modxmodfurnishings/modxmod-main/labs/experimental/F0617_TableInsert_StandBack.STEP

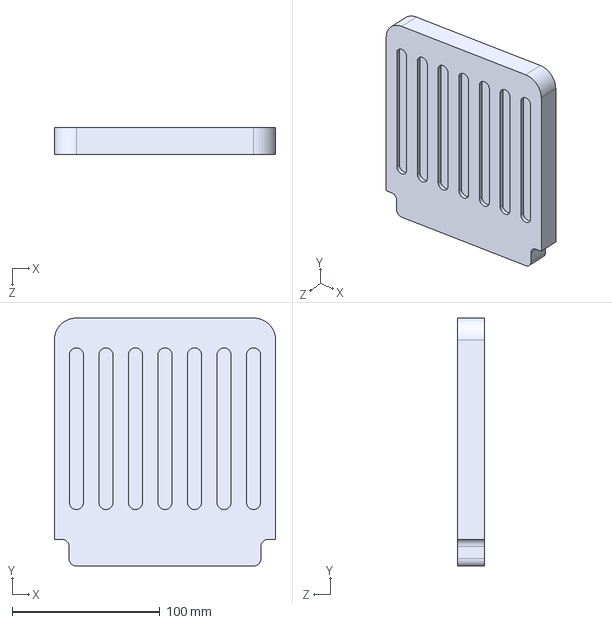
[picture p33: CAD file, 2024-06-18]
labs/experimental/F0617_TableInsert_StandBack.STEP
150.0 x 168.0 x 18.0 mm
