modxmodfurnishings/modxmod-main/labs/experimental/F0529_Span100_Wood_C2.STL

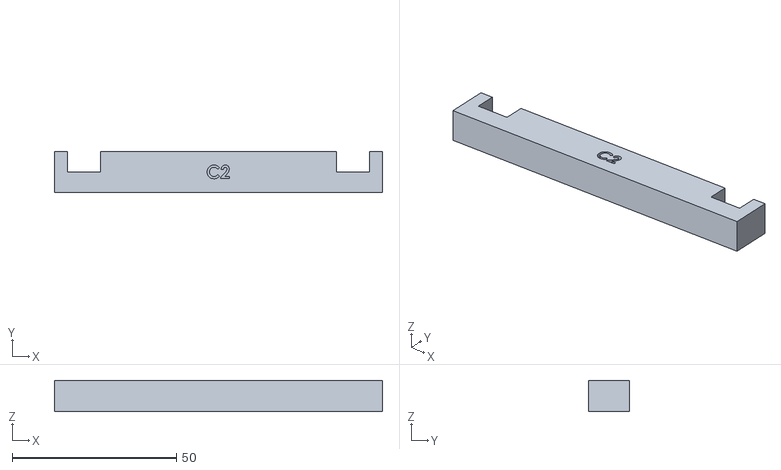
[picture p34: CAD file, 2024-05-30]
labs/experimental/F0529_Span100_Wood_C2.STL
100.0 x 12.6 x 9.50
