modxmodfurnishings/modxmod-main/labs/experimental/F0529_PostPlug_C.STL

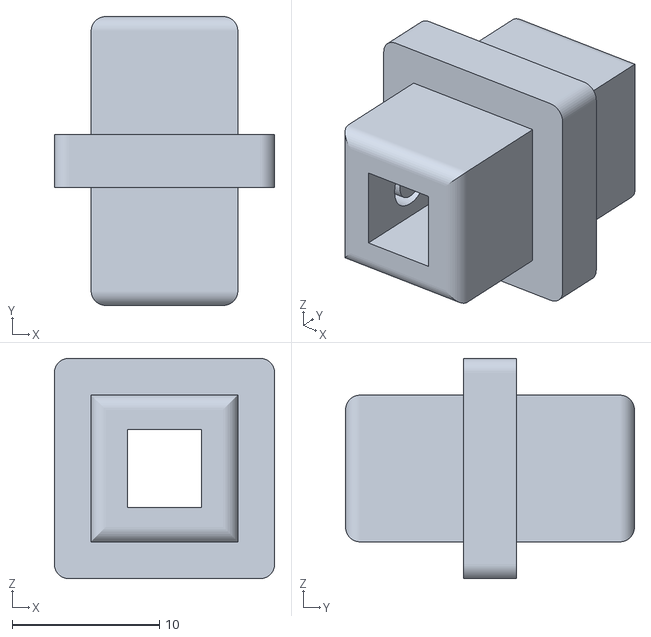
[picture p35: CAD file, 2024-05-30]
labs/experimental/F0529_PostPlug_C.STL
14.9 x 19.6 x 14.9
