modxmodfurnishings/modxmod-main/labs/experimental/F0529_Post80_Wood_C.STL

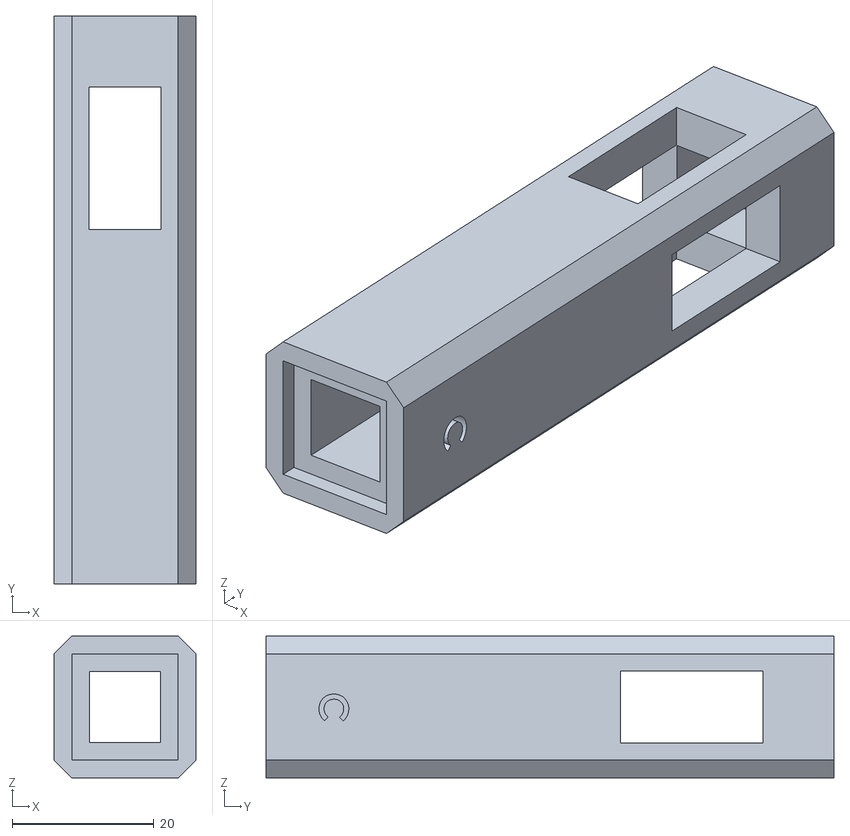
[picture p36: CAD file, 2024-05-30]
labs/experimental/F0529_Post80_Wood_C.STL
20.0 x 80.0 x 20.0
