modxmodfurnishings/modxmod-main/labs/experimental/Drawer Front XLatch Top (1).stl

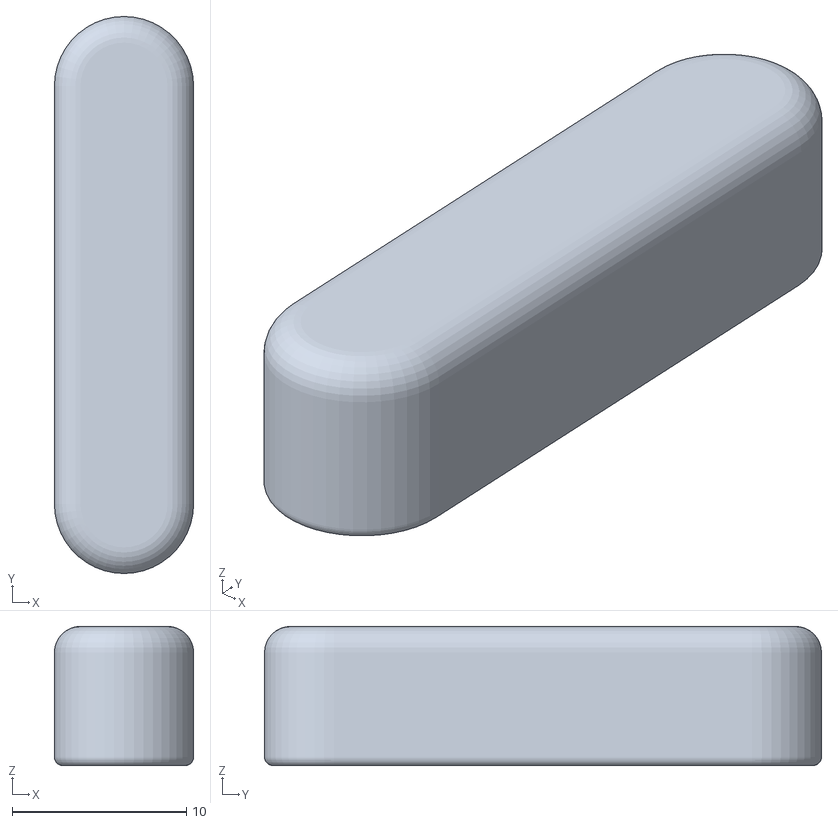
[picture p37: CAD file, 2024-04-15]
labs/experimental/Drawer Front XLatch Top (1).stl
8.00 x 32.0 x 8.00
