modxmodfurnishings/modxmod-main/labs/experimental/CabFrame Bar2.stl

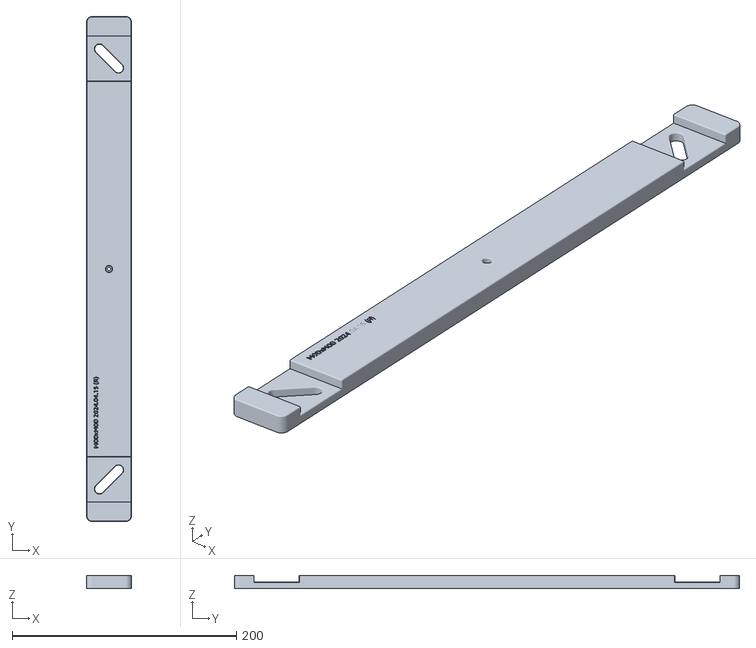
[picture p38: CAD file, 2024-04-15]
labs/experimental/CabFrame Bar2.stl
40.0 x 450.0 x 12.0
