modxmodfurnishings/modxmod-main/labs/experimental/CabFrame Corner2 (1).stl

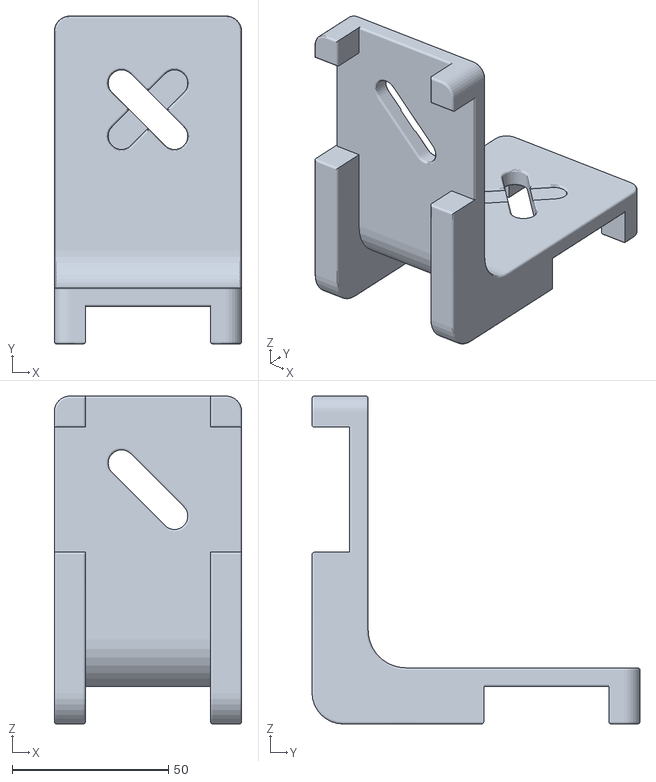
[picture p39: CAD file, 2024-04-15]
labs/experimental/CabFrame Corner2 (1).stl
60.0 x 105.0 x 105.0
