modxmodfurnishings/modxmod-main/labs/experimental/Drawer Front XLatch Test Wall 1 (1).stl

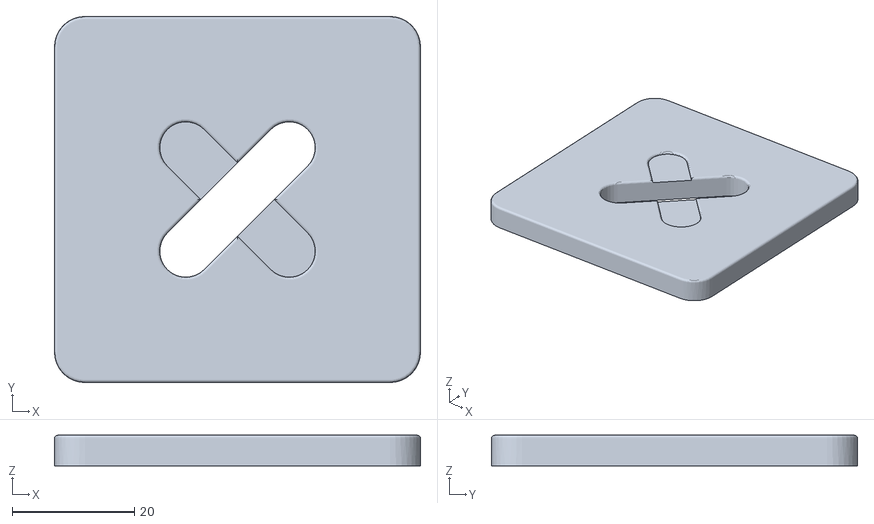
[picture p40: CAD file, 2024-04-15]
labs/experimental/Drawer Front XLatch Test Wall 1 (1).stl
60.0 x 60.0 x 5.00
