modxmodfurnishings/modxmod-main/labs/experimental/FurnNightst02a v5.stl

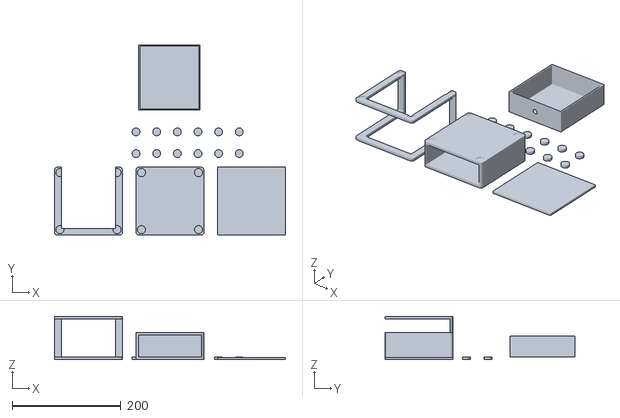
[picture p41: CAD file, 2024-03-26]
labs/experimental/FurnNightst02a v5.stl
425.0 x 350.0 x 80.0
