modxmodfurnishings/modxmod-main/labs/experimental/Pulls1 v8.stl

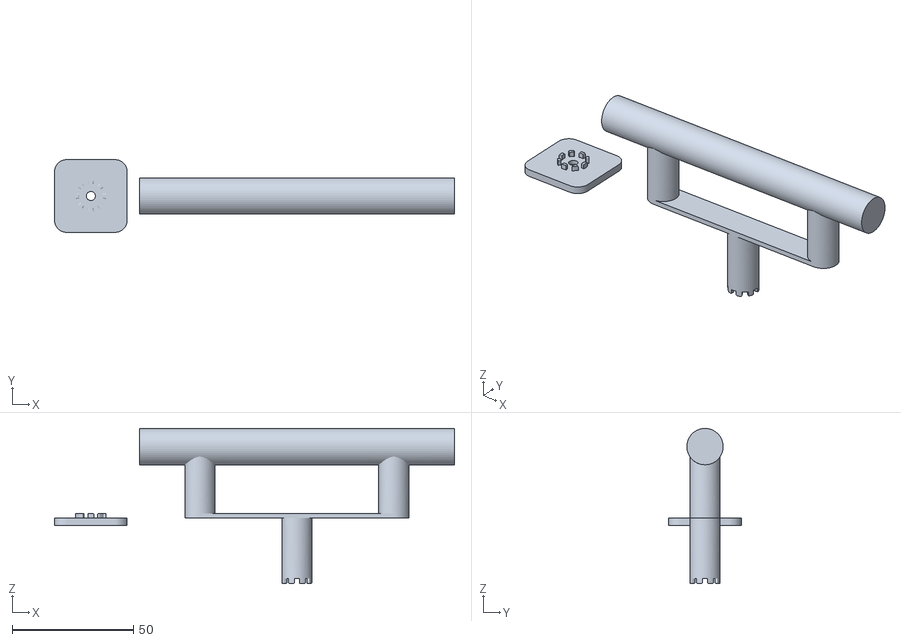
[picture p42: CAD file, 2024-03-26]
labs/experimental/Pulls1 v8.stl
165.0 x 30.0 x 64.0
