modxmodfurnishings/modxmod-main/labs/experimental/Pulls1 v6.3mf

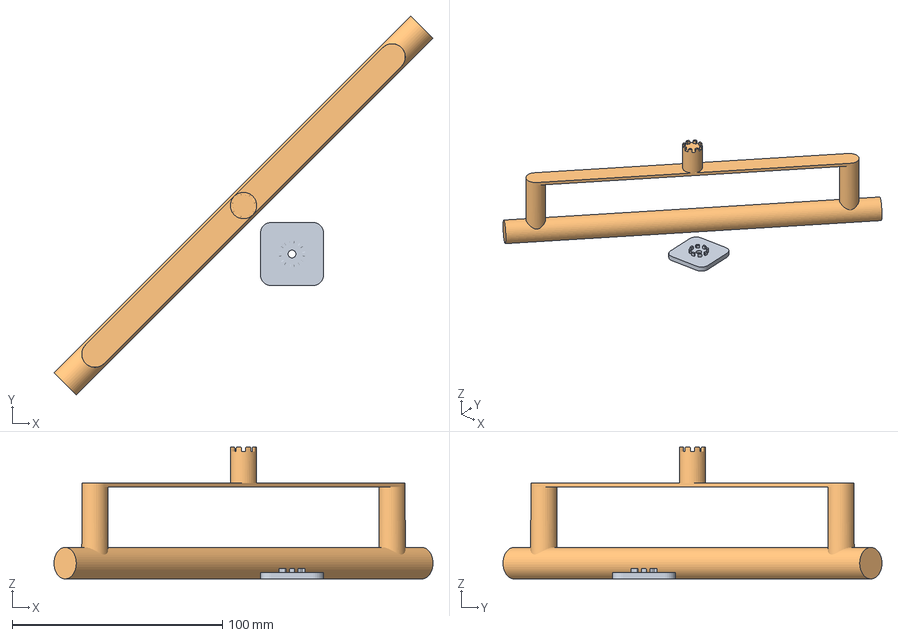
[picture p43: CAD file, 2024-03-26]
labs/experimental/Pulls1 v6.3mf
180.3 x 180.3 x 62.7 mm
Pulls1 v6.stl_1
Pulls1 v6.stl_2
