modxmodfurnishings/modxmod-main/labs/experimental/Furn1 v8.stl

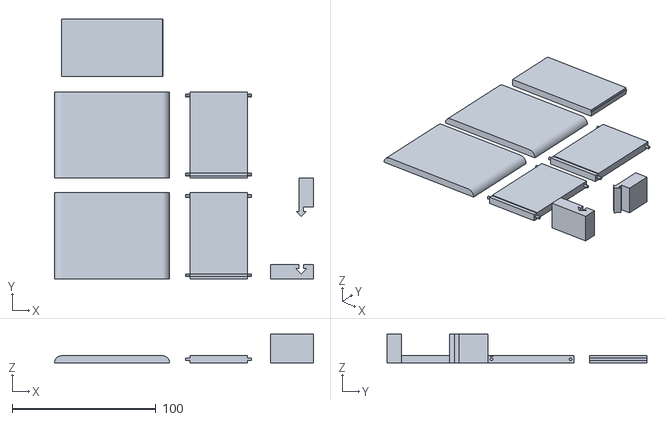
[picture p44: CAD file, 2024-03-24]
labs/experimental/Furn1 v8.stl
180.0 x 180.6 x 20.0
