modxmodfurnishings/modxmod-main/labs/experimental/Aligner v1.stl

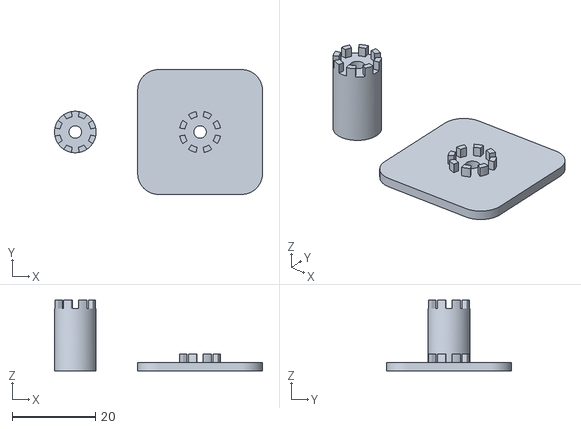
[picture p45: CAD file, 2024-03-24]
labs/experimental/Aligner v1.stl
50.0 x 30.0 x 17.0
