modxmodfurnishings/modxmod-main/labs/experimental/TeethKnobTri1.stl

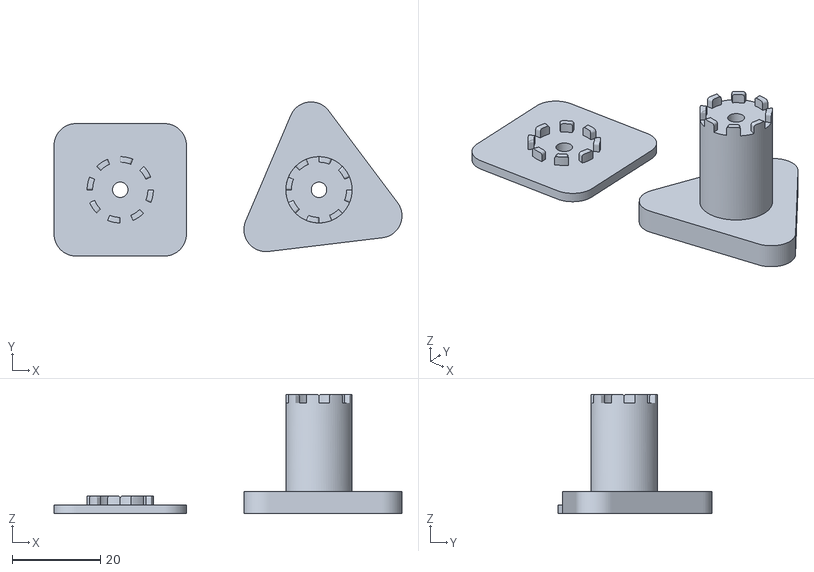
[picture p46: CAD file, 2024-03-24]
labs/experimental/TeethKnobTri1.stl
78.8 x 34.9 x 27.0
