modxmodfurnishings/modxmod-main/labs/experimental/Furn2 v6 bamboo front only.3mf

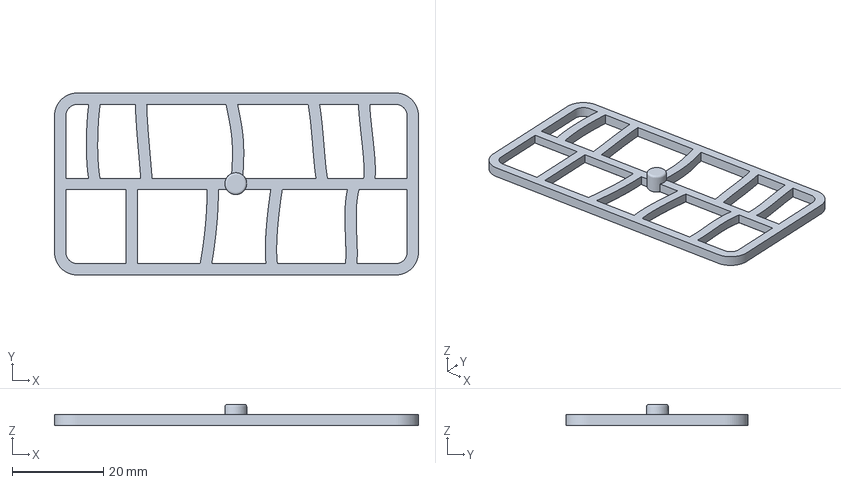
[picture p47: CAD file, 2024-03-24]
labs/experimental/Furn2 v6 bamboo front only.3mf
79.7 x 39.9 x 4.70 mm
