modxmodfurnishings/modxmod-main/labs/experimental/Furn3 v21.stl

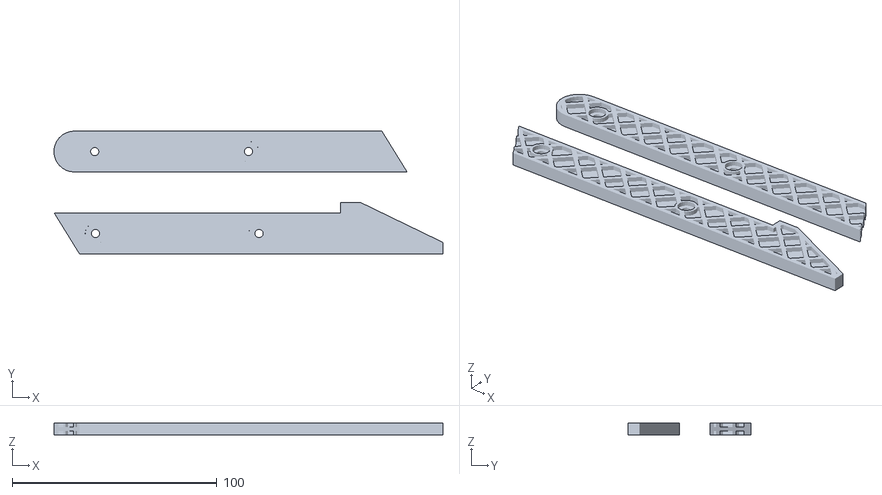
[picture p48: CAD file, 2024-03-24]
labs/experimental/Furn3 v21.stl
189.9 x 60.0 x 6.00
