modxmodfurnishings/modxmod-main/labs/experimental/Furn2 v6.stl

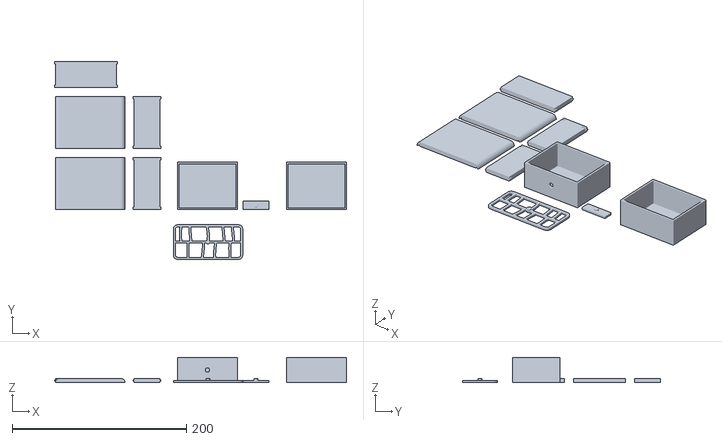
[picture p49: CAD file, 2024-03-24]
labs/experimental/Furn2 v6.stl
335.0 x 227.0 x 29.0
