modxmodfurnishings/modxmod-main/labs/experimental/Furn3 v3.step

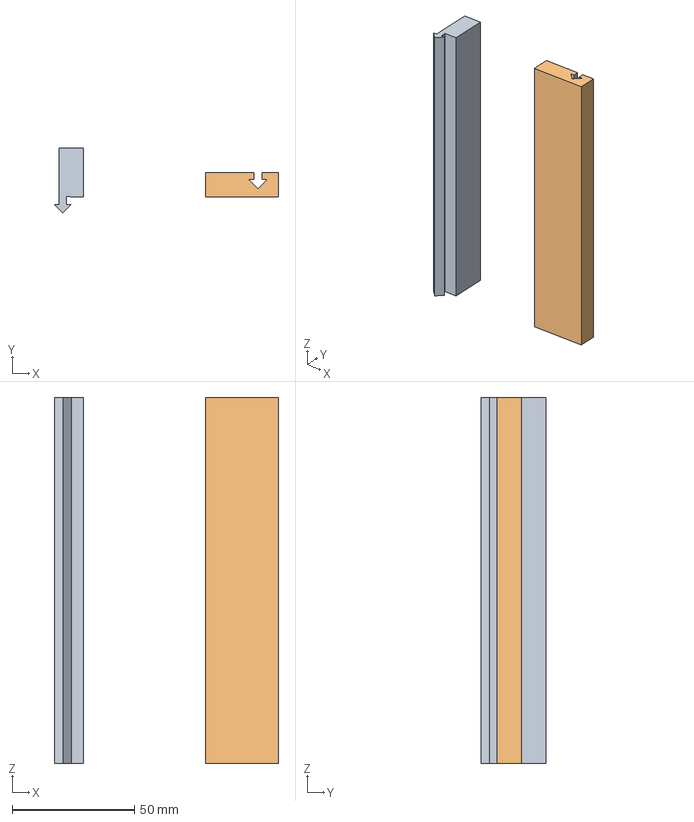
[picture p50: CAD file, 2024-03-24]
labs/experimental/Furn3 v3.step
92.0 x 26.5 x 150.0 mm
