modxmodfurnishings/modxmod-main/labs/experimental/F0605-full-assembly.png

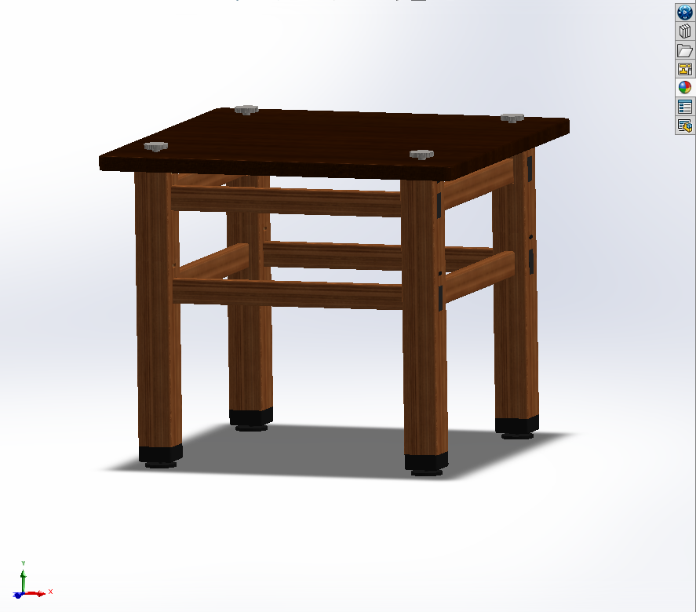
labs/experimental/F0605-full-assembly.png
