modxmodfurnishings/modxmod-main/labs/experimental/F0605-post-assembly.png

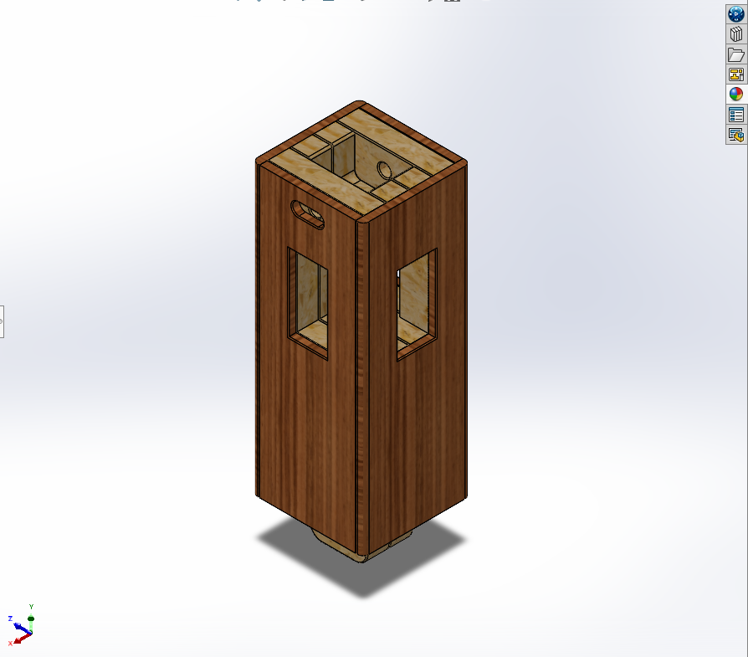
labs/experimental/F0605-post-assembly.png
