modxmodfurnishings/modxmod-main/labs/experimental/B384-exploded.jpg

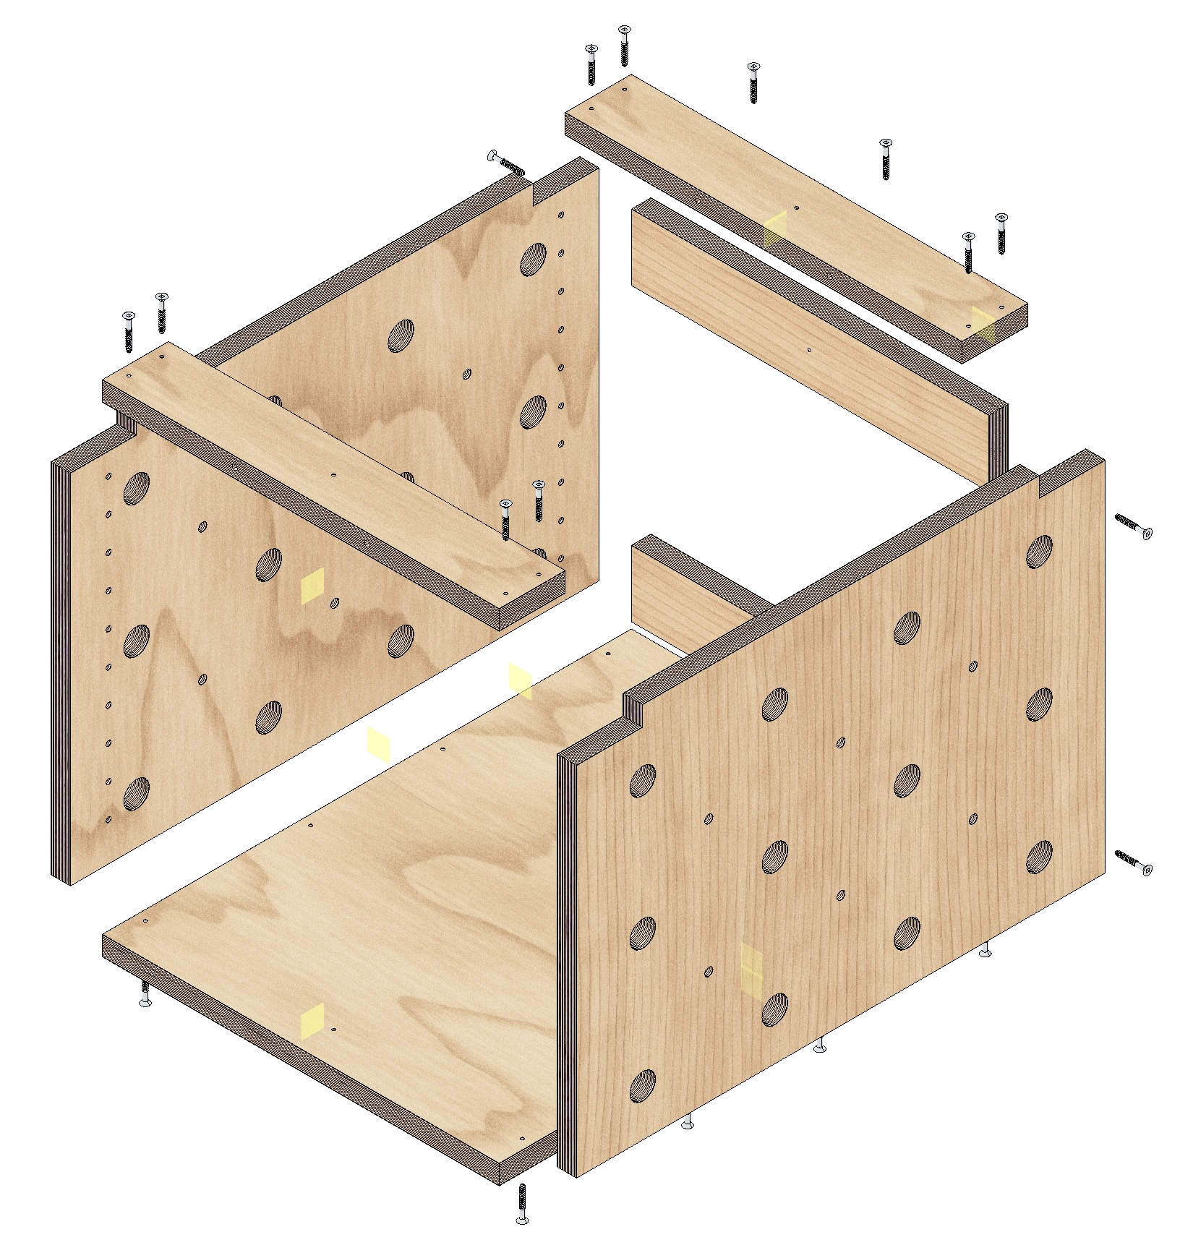
labs/experimental/B384-exploded.jpg
