modxmodfurnishings/modxmod-main/labs/experimental/B384-together.jpg

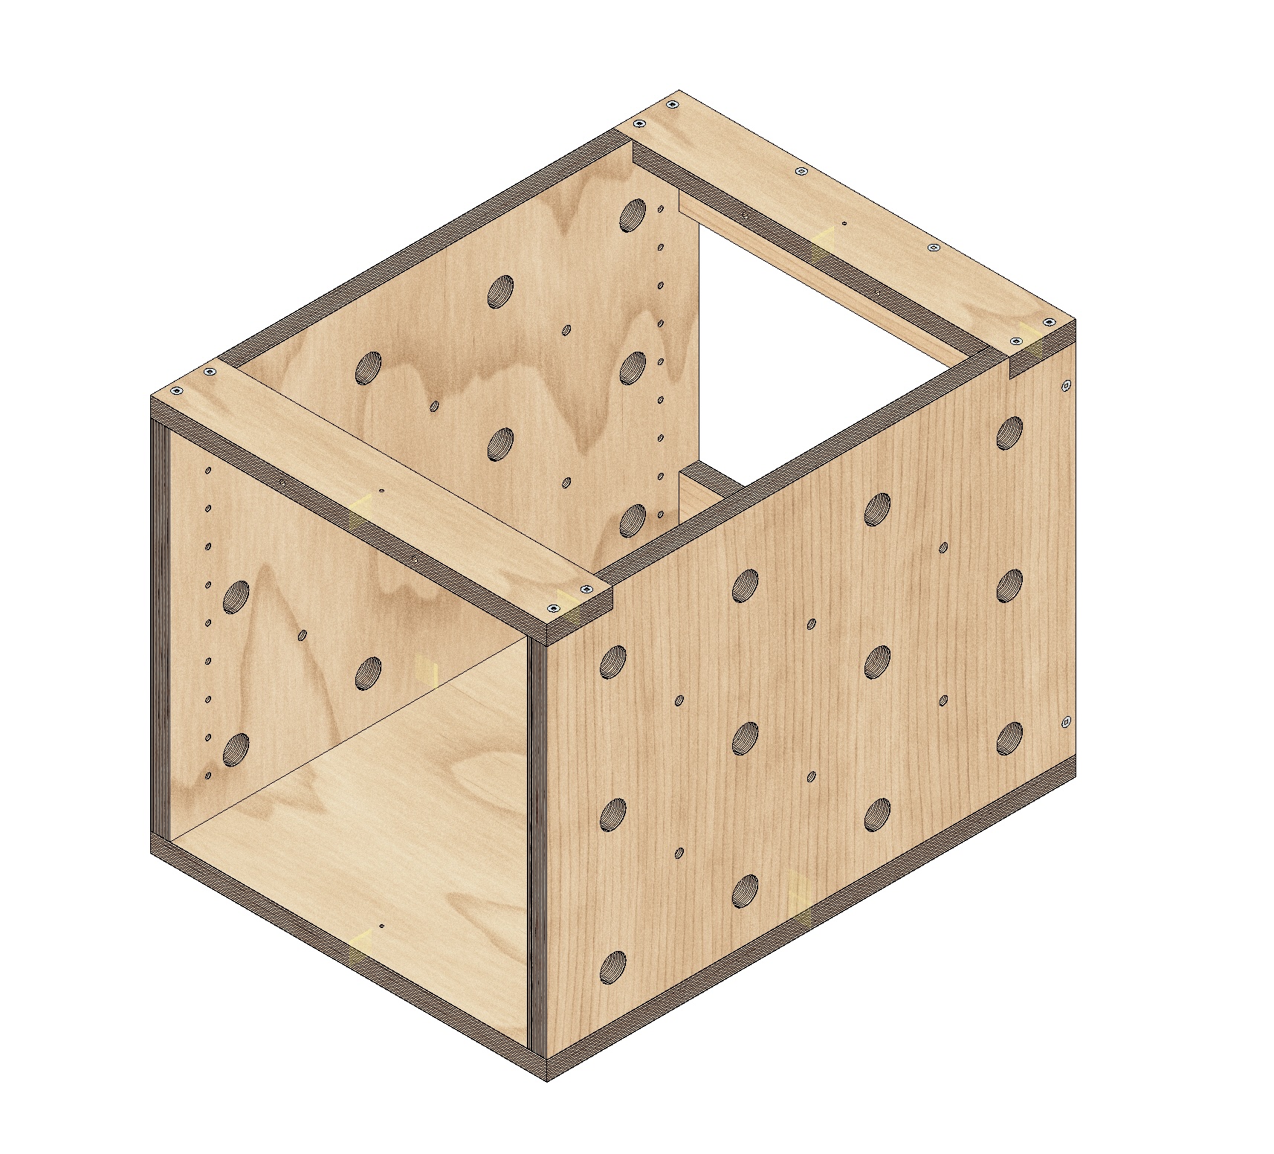
labs/experimental/B384-together.jpg
