modxmodfurnishings/modxmod-main/labs/experimental/F0605-lap-pin.png

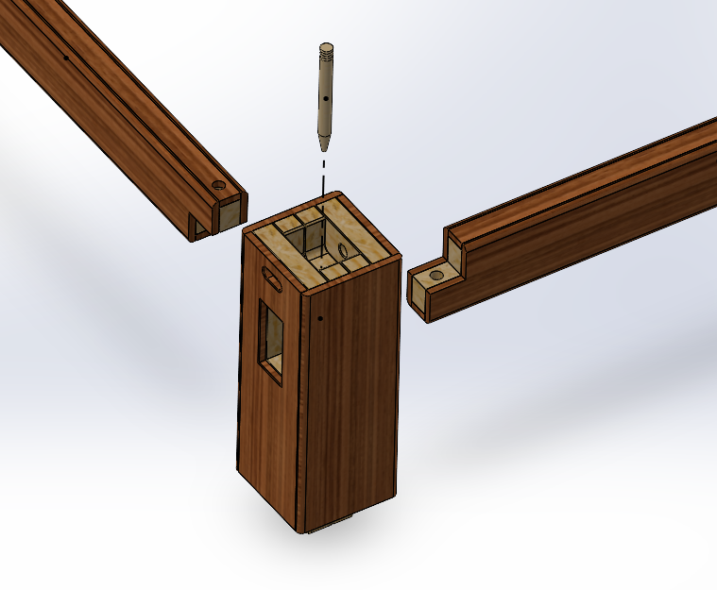
labs/experimental/F0605-lap-pin.png
