modxmodfurnishings/modxmod-main/labs/experimental/F0605-post-exploded.png

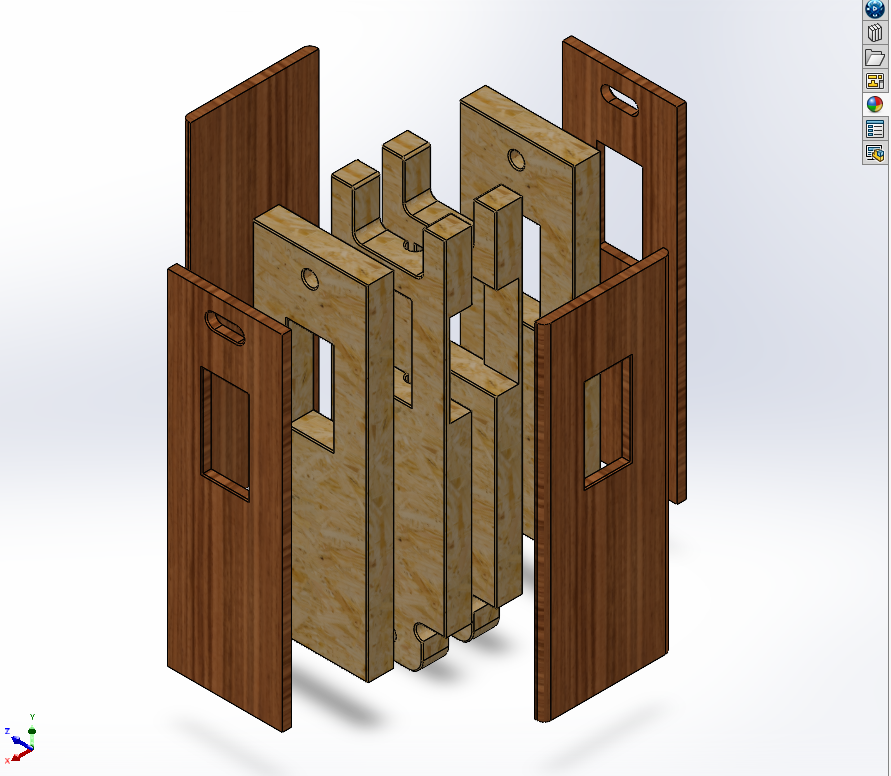
labs/experimental/F0605-post-exploded.png
