modxmodfurnishings/modxmod-main/labs/experimental/F0618_Screenshot_TestLayout.png

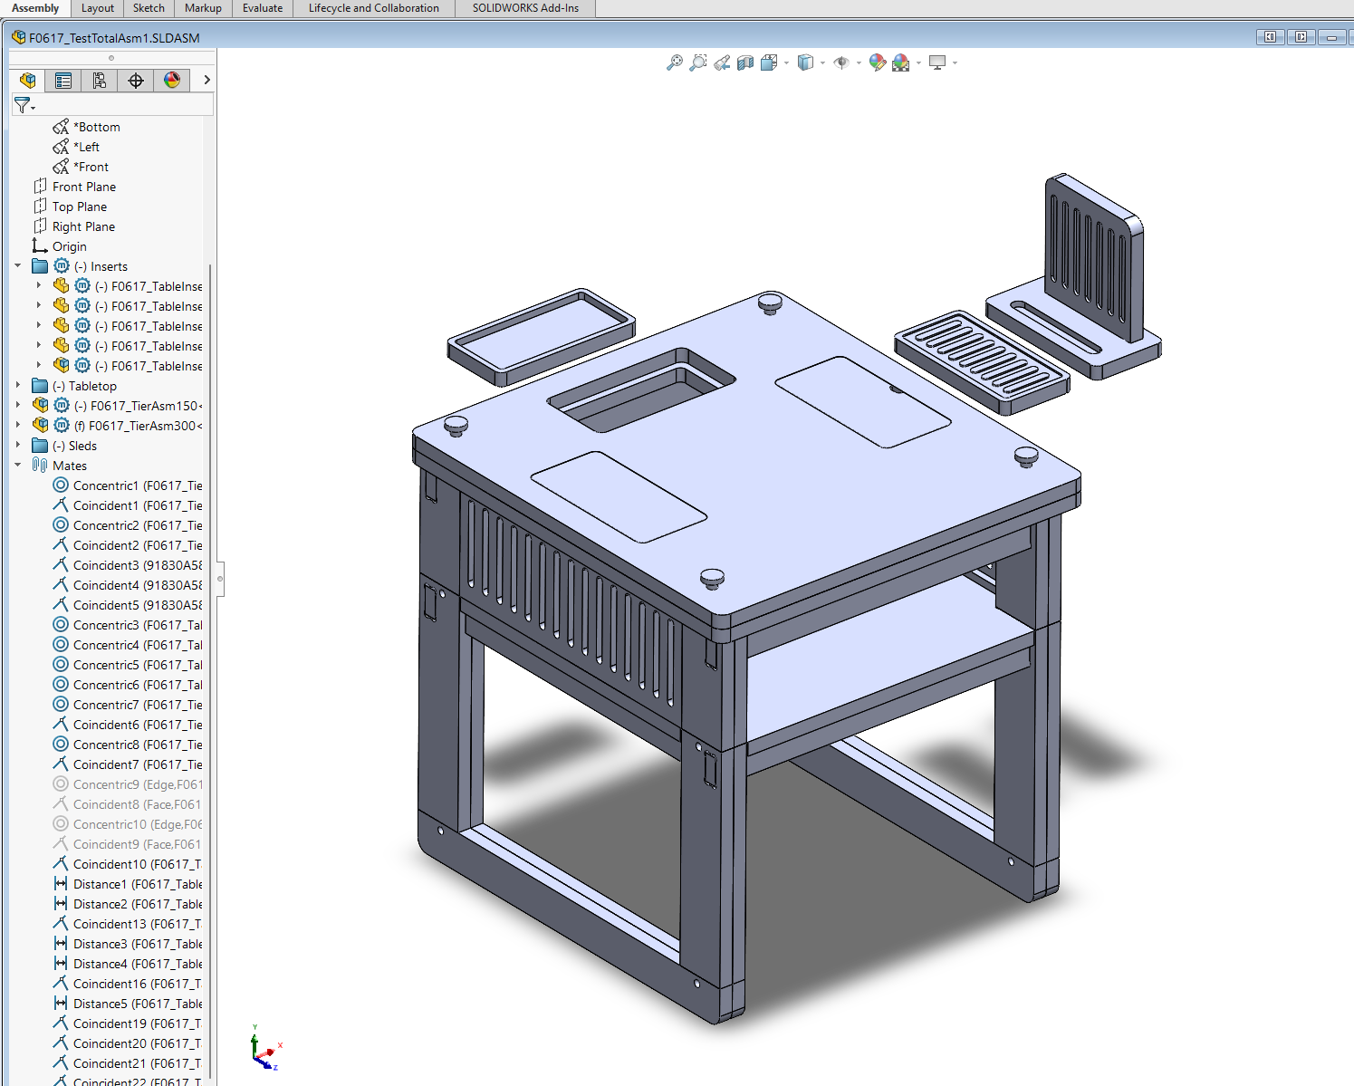
labs/experimental/F0618_Screenshot_TestLayout.png
