modxmodfurnishings/modxmod-main/labs/experimental/F0717_Box375_Scr01.png

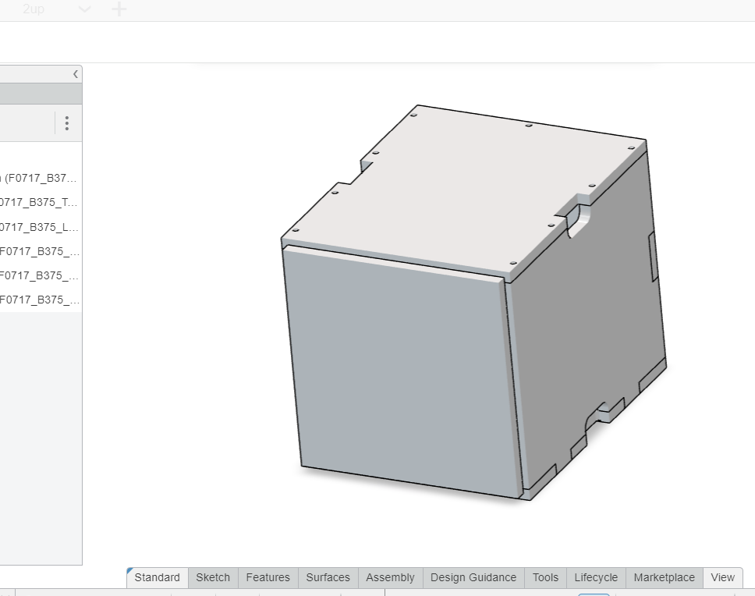
labs/experimental/F0717_Box375_Scr01.png
