modxmodfurnishings/modxmod-main/labs/experimental/F0717_Box375_Scr02.png

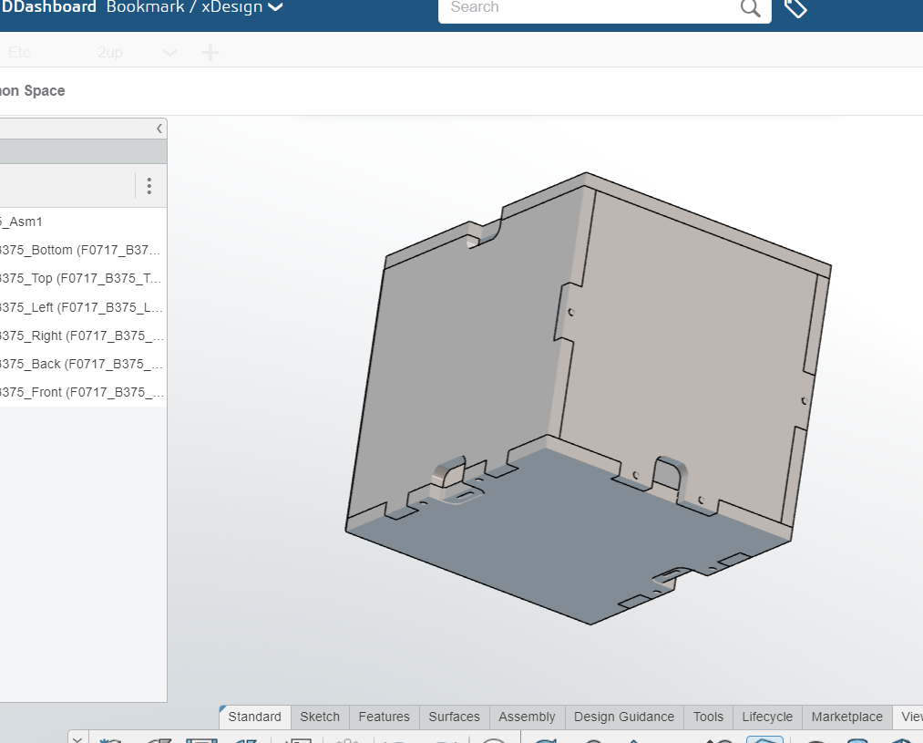
labs/experimental/F0717_Box375_Scr02.png
