modxmodfurnishings/modxmod-main/labs/experimental/F0717_Box375_Scr03.png

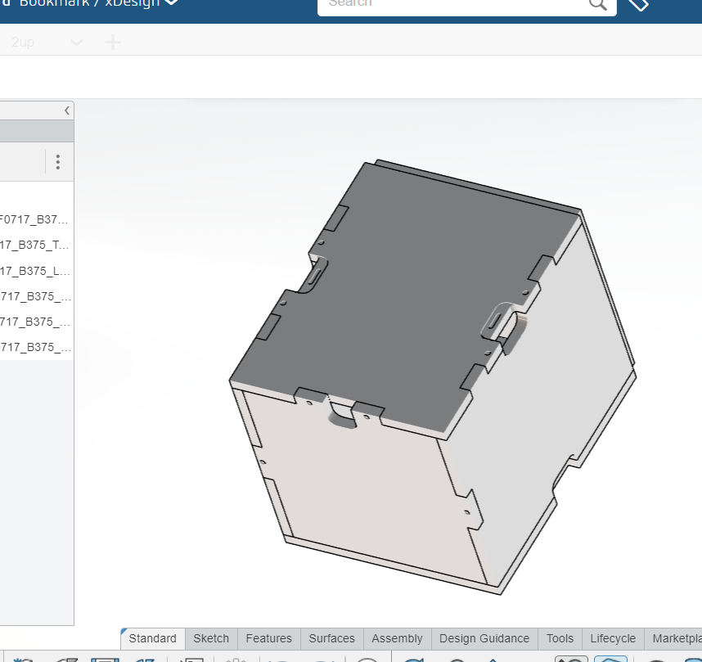
labs/experimental/F0717_Box375_Scr03.png
