modxmodfurnishings/modxmod-main/labs/experimental/F1125_393Box_268Box_143Box.png

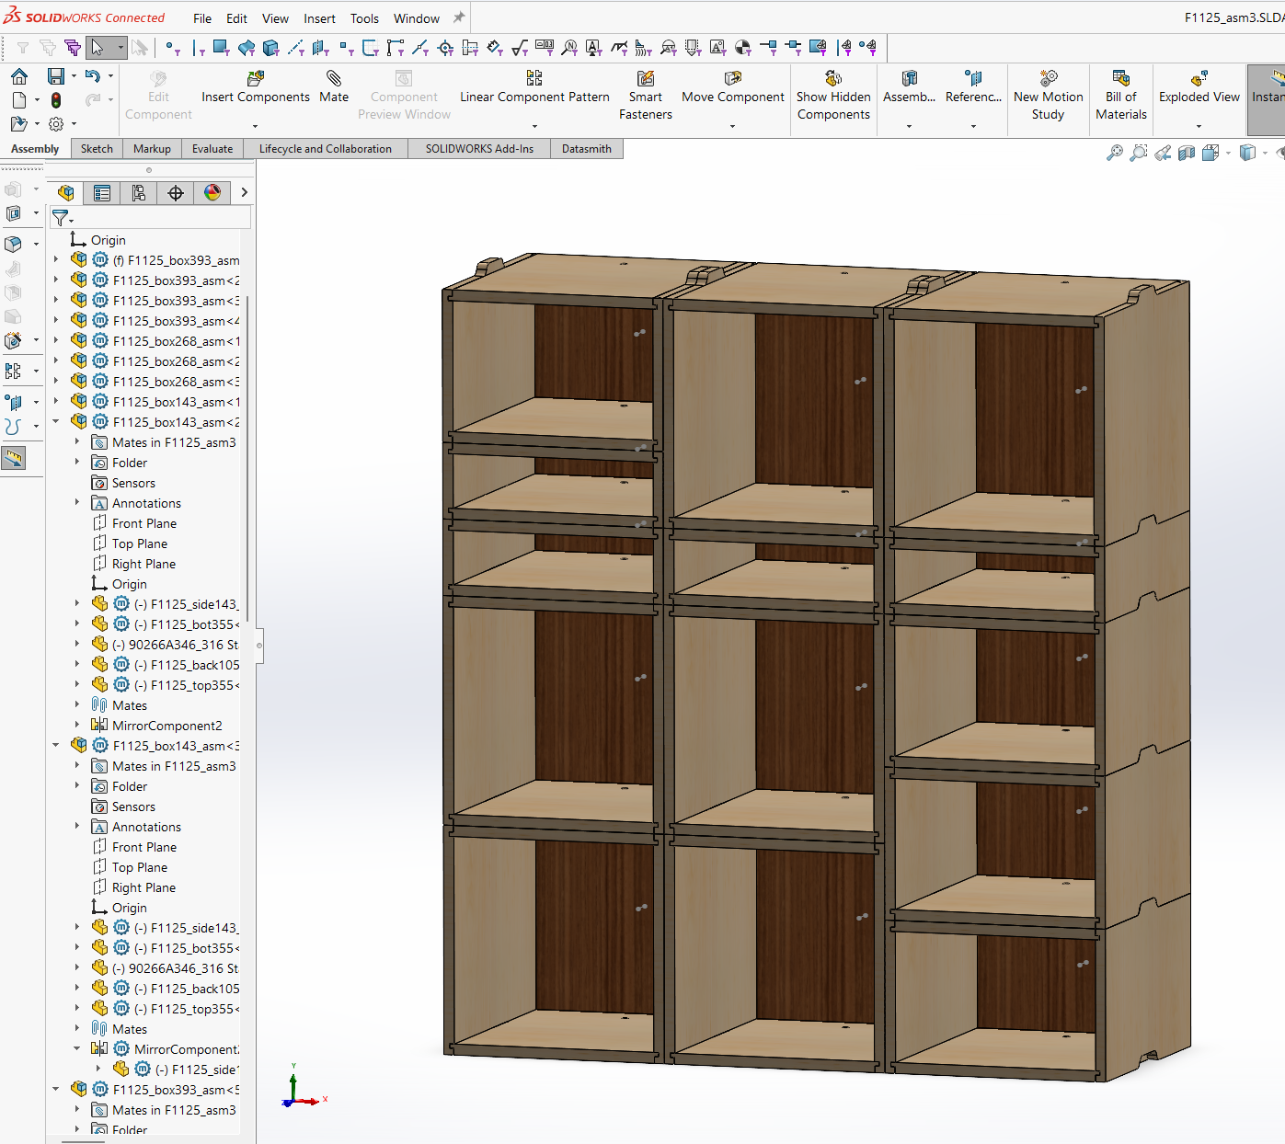
labs/experimental/F1125_393Box_268Box_143Box.png
