modxmodfurnishings/modxmod-main/labs/experimental/F1125_393BoxStack1.png

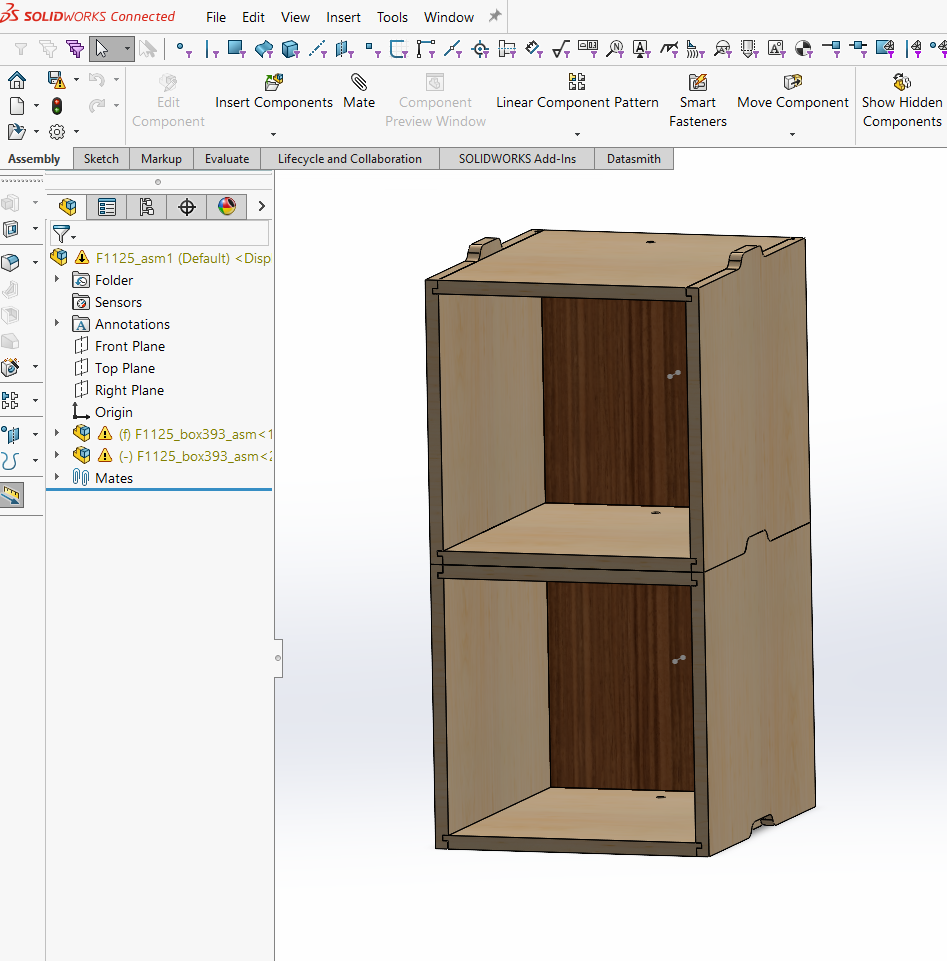
labs/experimental/F1125_393BoxStack1.png
