modxmodfurnishings/modxmod-main/labs/experimental/Furn4.jpg

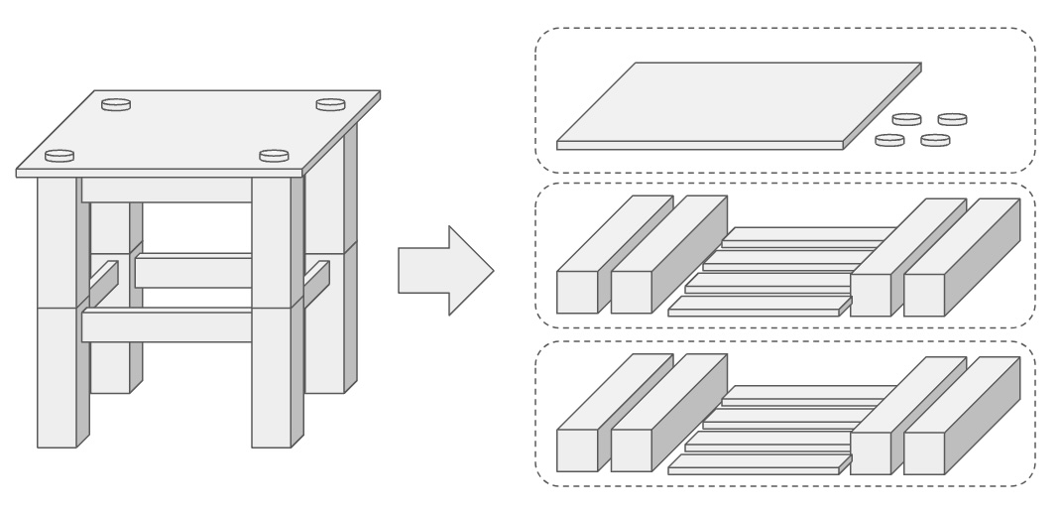
labs/experimental/Furn4.jpg
