modxmodfurnishings/modxmod-main/labs/experimental/simple-template-20240324a-pulls.png

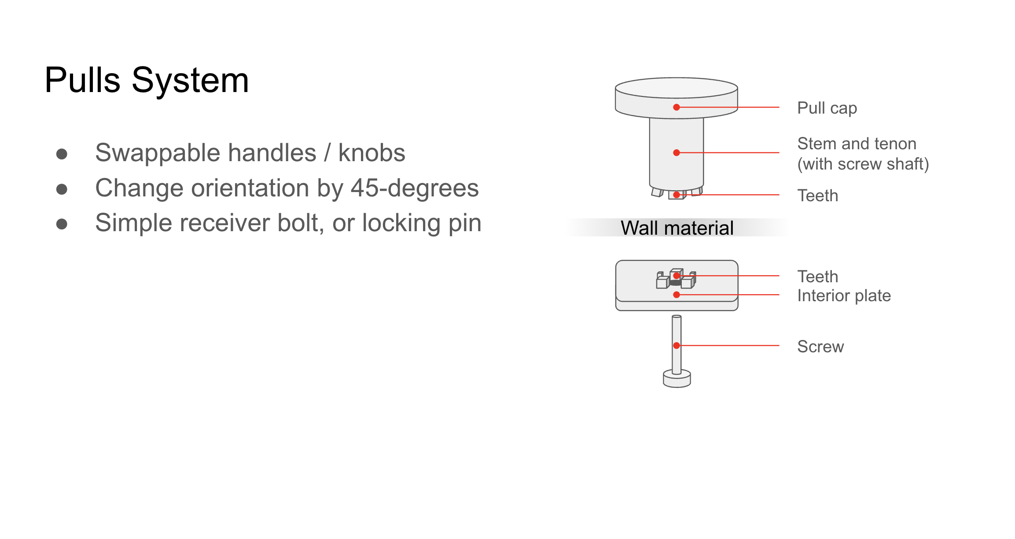
labs/experimental/simple-template-20240324a-pulls.png
