modxmodfurnishings/modxmod-main/labs/experimental/T0129_3BaseRender.png

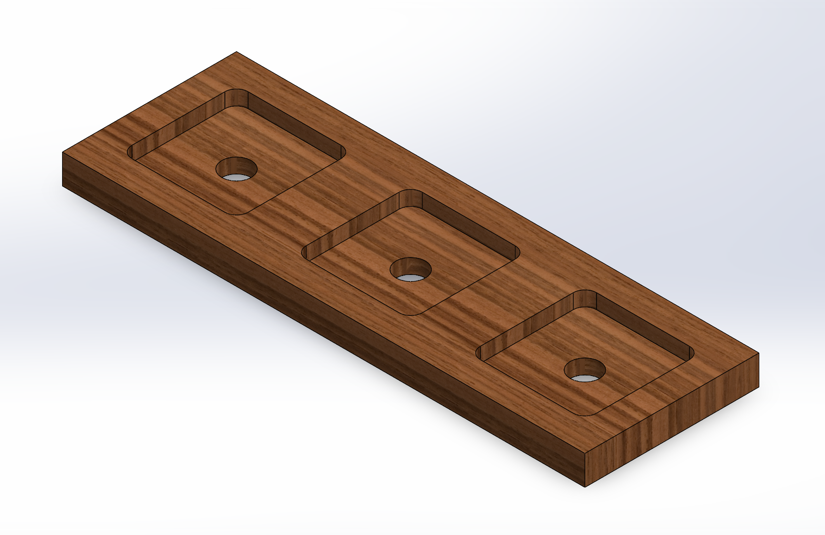
labs/experimental/T0129_3BaseRender.png
